jvok94/powered-speaker/Simulation/amp.asc

C1: cap; 100pF
C2: cap; 1µF
C3: cap; 100pF
C4: cap; 470pF
C6: cap; 10µF
C8: cap; 100nF
D1: diode; 1N4148
D2: diode; 1N4148
D3: diode; 1N4148
D4: diode; 1N4148
Q1: npn; BC546B
Q2: pnp; MJE15031
Q3: npn; MJE15030
Q4: pnp; BC556B
Q5: pnp; BC556B
Q6: npn; BC546B
Q7: npn; BC546B
Q8: pnp; BC556B
Q9: pnp; BC556B
Q10: npn; BC546B
Q11: npn; BC546B
Q12: npn; BC546B
R1: res; 0.33
R2: res; 0.33
R3: res; 220
R4: res; 220
R5: res; 1.2k
R6: res; 1352
R7: res; 100
R8: res; 12k
R9: res; 270
R10: res; 270
R11: res; 470
R12: res; 12k
R13: res; 2.2k
R14: res; 68k
R15: res; 4
R21: res; 68k
R22: res; 4k7
R23: res; 10
R25: res; 220
V1: voltage; 25.5
V2: voltage; SINE(0 0 1k)
V3: voltage; 25.5
Named nets: 0
.tran 0 10m 0
